Ruslanyus/Oddjob/Code/oddjob/data/astro copie.jpg

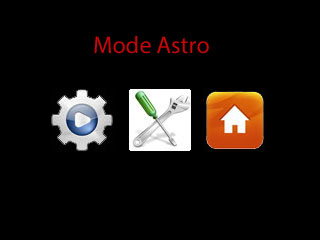
Code/oddjob/data/astro copie.jpg
