Ruslanyus/Oddjob/Code/oddjob/data/menu copie.jpg

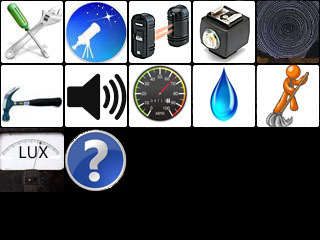
Code/oddjob/data/menu copie.jpg
