Ruslanyus/Oddjob/Code/oddjob/data/system copie.jpg

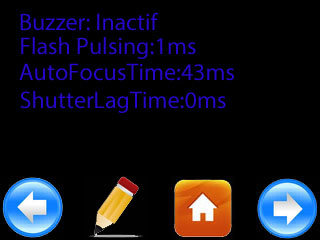
Code/oddjob/data/system copie.jpg
