Ruslanyus/Oddjob/Code/oddjob/data/water_mode.jpg

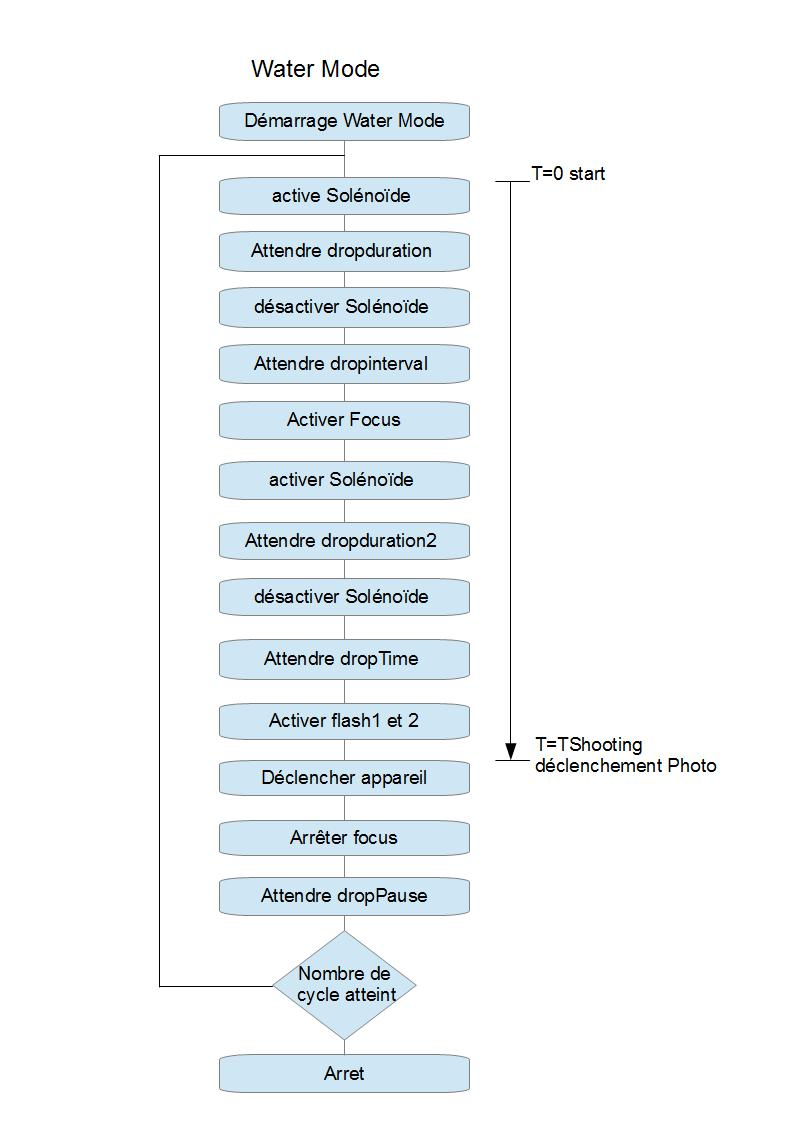
Code/oddjob/data/water_mode.jpg
