Ruslanyus/Oddjob/Code/oddjob/runmode_audiotrigger.ino

/**
 *
 * - Oddjob
 *
 * This file is part of Oddjob based on the Photoduino.
 *
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
 * You should have received a copy of the GNU General Public License
 * along with Oddjob.  If not, see <http://www.gnu.org/licenses/>.
 */
  
  
  

// Load the audioTriggerMode from eeprom to ram
void config_loadBackup_audioTriggerMode(){   
  
  audioTriggerMode_shootingMode = EEPROM.read(EE_ADDR_audioTriggerMode_shootingMode);
  audioTriggerMode_sensorLimit = eeprom_readInt(EE_ADDR_audioTriggerMode_sensorLimit);
  audioTriggerMode_autofocusTime = eeprom_readInt(EE_ADDR_audioTriggerMode_autofocusTime);
  audioTriggerMode_shutterLagTime = eeprom_readInt(EE_ADDR_audioTriggerMode_shutterLagTime);
  audioTriggerMode_preCloseTime = eeprom_readInt(EE_ADDR_audioTriggerMode_preCloseTime);
  audioTriggerMode_useFlash1 = EEPROM.read(EE_ADDR_audioTriggerMode_useFlash1);
  audioTriggerMode_preFlash1Time = eeprom_readInt(EE_ADDR_audioTriggerMode_preFlash1Time);
  audioTriggerMode_useFlash2 = EEPROM.read(EE_ADDR_audioTriggerMode_useFlash2);
  audioTriggerMode_preFlash2Time = eeprom_readInt(EE_ADDR_audioTriggerMode_preFlash2Time);
  audioTriggerMode_numCicles =  eeprom_readInt(EE_ADDR_audioTriggerMode_numCicles);
  audioTriggerMode_interCicleTime =  eeprom_readInt(EE_ADDR_audioTriggerMode_interCicleTime);
}

// Load the default audioTriggerMode config to ram
void config_loadDefaults_audioTriggerMode() {
  
  audioTriggerMode_shootingMode =     DEFAULT_audioTriggerMode_shootingMode;
  audioTriggerMode_sensorLimit =      DEFAULT_audioTriggerMode_sensorLimit;
  audioTriggerMode_autofocusTime =    DEFAULT_audioTriggerMode_autofocusTime;
  audioTriggerMode_shutterLagTime =   DEFAULT_audioTriggerMode_shutterLagTime;
  audioTriggerMode_preCloseTime =     DEFAULT_audioTriggerMode_preCloseTime;
  audioTriggerMode_useFlash1 =        DEFAULT_audioTriggerMode_useFlash1;
  audioTriggerMode_preFlash1Time =    DEFAULT_audioTriggerMode_preFlash1Time;
  audioTriggerMode_useFlash2 =        DEFAULT_audioTriggerMode_useFlash2;
  audioTriggerMode_preFlash2Time =    DEFAULT_audioTriggerMode_preFlash2Time;
  audioTriggerMode_numCicles =        DEFAULT_audioTriggerMode_numCicles;
  audioTriggerMode_interCicleTime =   DEFAULT_audioTriggerMode_interCicleTime;
}

// Save the audioTriggerMode from ram to eeprom
void config_saveBackup_audioTriggerMode(){ 
  
  EEPROM.write(EE_ADDR_audioTriggerMode_shootingMode, audioTriggerMode_shootingMode);
  eeprom_writeInt(EE_ADDR_audioTriggerMode_sensorLimit, audioTriggerMode_sensorLimit);
  eeprom_writeInt(EE_ADDR_audioTriggerMode_autofocusTime, audioTriggerMode_autofocusTime);
  eeprom_writeInt(EE_ADDR_audioTriggerMode_shutterLagTime, audioTriggerMode_shutterLagTime);
  eeprom_writeInt(EE_ADDR_audioTriggerMode_preCloseTime, audioTriggerMode_preCloseTime);
  EEPROM.write(EE_ADDR_audioTriggerMode_useFlash1, audioTriggerMode_useFlash1);
  eeprom_writeInt(EE_ADDR_audioTriggerMode_preFlash1Time, audioTriggerMode_preFlash1Time);
  EEPROM.write(EE_ADDR_audioTriggerMode_useFlash2, audioTriggerMode_useFlash2);
  eeprom_writeInt(EE_ADDR_audioTriggerMode_preFlash2Time, audioTriggerMode_preFlash2Time);
  eeprom_writeInt(EE_ADDR_audioTriggerMode_numCicles, audioTriggerMode_numCicles);
  eeprom_writeInt(EE_ADDR_audioTriggerMode_interCicleTime, audioTriggerMode_interCicleTime); 
}

  
  
  int menu_audio()
{
   int res;

  while (true)
  {
  
  res=mode_menu("Mode Audio");
   switch(res)
  {
    case 0: //run
    //res2=menu_conf_interval();
    runAs_audioTrigger();
    break;
    
    case 1: //config
     menu_conf_audio();
     config_saveBackup_audioTriggerMode();
     
    break;
    
    case 2: //home
    return(0);
    break;
  }
  }
}

int menu_conf_audio()
{
  struct list_data list[9];
  
  list[0].description="Sensor Limit";
  list[0].unit=" ";
  list[0].value=audioTriggerMode_sensorLimit;
  list[0].mini=PINS_SENSOR_MIC;
  list[0].maxi=PINS_SENSOR_MIC;
  list[0].list[0]="";
  list[0].list[1]="";
  list[0].list[3]="";
  list[0].list[4]="Sensor";

  list[1].description="Shooting Mode";
  list[1].unit=" ";
  list[1].value=audioTriggerMode_shootingMode;
  list[1].mini=0;
  list[1].maxi=1;
  list[1].list[0]="Normal";
  list[1].list[1]="Pre-Bulb";
  list[1].list[3]="Mirror Lock-ip";
  list[1].list[4]="Pre Focused";
  
  
  list[2].description="Use Flash1";
  list[2].unit=" ";
  list[2].value=audioTriggerMode_useFlash1;
  list[2].mini=0;
  list[2].maxi=1;
  list[2].list[0]="Actif";
  list[2].list[1]="Inactif";
  list[2].list[3]="";
  list[2].list[4]="";

  list[3].description="PreFlash1Time";
  list[3].unit="ms";
  list[3].value=audioTriggerMode_preFlash1Time;
  list[3].mini=0;
  list[3].maxi=1000;
  list[3].list[0]="";
  list[3].list[1]="";
  list[3].list[2]="";
  list[3].list[3]="";
  list[3].list[4]="";

  list[4].description="Use Flash2";
  list[4].unit=" ";
  list[4].value=audioTriggerMode_useFlash2;
  list[4].mini=0;
  list[4].maxi=1;
  list[4].list[0]="Actif";
  list[4].list[1]="Inactif";
  list[4].list[2]="";
  list[4].list[3]="";
  list[4].list[4]="";

  list[5].description="PreFlash2 Time";
  list[5].unit="ms";
  list[5].value=audioTriggerMode_preFlash2Time;
  list[5].mini=0;
  list[5].maxi=1000;
  list[5].list[0]="";
  list[5].list[1]="";
  list[5].list[2]="";
  list[5].list[3]="";
  list[5].list[4]="";

  list[6].description="PreClose Time";
  list[6].unit="ms";
  list[6].value=audioTriggerMode_preCloseTime;
  list[6].mini=0;
  list[6].maxi=1000;
  list[6].list[0]="";
  list[6].list[1]="";
  list[6].list[2]="";
  list[6].list[3]="";
  list[6].list[4]="";

  list[7].description="Nb Cicles";
  list[7].unit="  ";
  list[7].value=audioTriggerMode_numCicles;
  list[7].mini=0;
  list[7].maxi=10000;
  list[7].list[0]="";
  list[7].list[1]="";
  list[7].list[2]="";
  list[7].list[3]="";
  list[7].list[4]="";

  list[8].description="Interval Time";
  list[8].unit="s ";
  list[8].value=audioTriggerMode_interCicleTime;
  list[8].mini=0;
  list[8].maxi=1000;
  list[8].list[0]="";
  list[8].list[1]="";
  list[8].list[2]="";
  list[8].list[3]="";
  list[8].list[4]="";
  
  
  
  myGLCD.clrScr();
  res=menu_list(9,list);
  audioTriggerMode_sensorLimit=list[0].value;
  audioTriggerMode_shootingMode=list[1].value;
  audioTriggerMode_useFlash1=list[2].value;
  audioTriggerMode_preFlash1Time=list[3].value;
  audioTriggerMode_useFlash2=list[4].value;
  audioTriggerMode_preFlash2Time=list[5].value;
  audioTriggerMode_preCloseTime=list[6].value;
  audioTriggerMode_numCicles=list[7].value;
  audioTriggerMode_interCicleTime=list[8].value;

  
  return(0);
}

 // Run audio trigger mode
void runAs_audioTrigger() {    
    
    int dec=20;
    int y=20;
    myGLCD.clrScr(); //clear the screen
    myGLCD.setFont(BigFont);
    myGLCD.setColor(200, 200, 200);
    myGLCD.print(MSG_RUN_AUDIO,10,y);
    y=y+dec;
    cancelFlag=false;
   
   for(unsigned int ciclesCounter = 0; (cancelFlag==false && !(audioTriggerMode_numCicles>0 && ciclesCounter >= audioTriggerMode_numCicles));ciclesCounter++) { 
     myGLCD.print("photo "+ String(ciclesCounter+1)+ "/" + String(audioTriggerMode_numCicles),10,y);
    
     // Normal shooting mode
     if (audioTriggerMode_shootingMode == 0) {
       
       sensor_waitFor(PINS_SENSOR_MIC, SENSOR_MODE_HIGHER, audioTriggerMode_sensorLimit, 0);
       
       if(!cancelFlag) {
         
         camera_autofocusBegin(audioTriggerMode_autofocusTime); 
         camera_shutterBegin(audioTriggerMode_shutterLagTime); 
          
         if (audioTriggerMode_useFlash1==0) flash_shoot(audioTriggerMode_preFlash1Time, PINS_FLASH1);
         if (audioTriggerMode_useFlash2==0) flash_shoot(audioTriggerMode_preFlash2Time, PINS_FLASH2); 

       }
     }  
     
     // Prebulb shooting mode
     if (audioTriggerMode_shootingMode == 1) {
      
       // With prebulb
       camera_autofocusBegin(audioTriggerMode_autofocusTime);
       camera_shutterBegin(audioTriggerMode_shutterLagTime); 
       
       sensor_waitFor(PINS_SENSOR_MIC, SENSOR_MODE_HIGHER, audioTriggerMode_sensorLimit, 0);
       
       if(!cancelFlag) {
         if (audioTriggerMode_useFlash1==0) flash_shoot(audioTriggerMode_preFlash1Time, PINS_FLASH1);
         if (audioTriggerMode_useFlash2==0) flash_shoot(audioTriggerMode_preFlash2Time, PINS_FLASH2);     
       }          
     }  
     
      // Mirror lock-up shooting mode
     if (audioTriggerMode_shootingMode == 3) {
              
       for(boolean result = false; result == false;  ){      
         camera_mirrorLockUp(audioTriggerMode_autofocusTime, audioTriggerMode_shutterLagTime);
         result = sensor_waitFor(PINS_SENSOR_MIC, SENSOR_MODE_HIGHER, audioTriggerMode_sensorLimit, DEVICES_CAMERA_MIRROR_LOCKUP_TIMELIMIT);
       }
       camera_shutterBegin(1); 
      
       if(!cancelFlag) {
         
         if (audioTriggerMode_useFlash1==0) flash_shoot(audioTriggerMode_preFlash1Time, PINS_FLASH1);
         if (audioTriggerMode_useFlash2==0) flash_shoot(audioTriggerMode_preFlash2Time, PINS_FLASH2); 
       }          
     }
    
     // Common for all shooting modes
     camera_shutterEnd(audioTriggerMode_preCloseTime); 
     camera_autofocusEnd();
     if(!cancelFlag) delay(audioTriggerMode_interCicleTime);
     cancelFlag=myTouch.dataAvailable();

   } 
    //cancelFlag=myTouch.dataAvailable();
  
}
